EnAccess/Cicada-GSM-HW/design/source/ltspice/Power.asc

C1: cap; 680µ
C2: cap; 680µ
C3: cap; 680µ
C4: cap; 680µ
C5: cap; 10µF
C6: cap; 10µF
C7: cap; 470p
C8: cap; 220µ
C9: cap; 220µ
C10: cap; 220µ
C11: cap; 10µF
D2: schottky; SS24
I1: load; PULSE(0.01A 2A 20ms 0 0 577us 5.192ms 1000)
L1: ind; 220µ; Rser=.1
R1: res; .08
R2: res; 0.08
R3: res; 0.08
R4: res; 0.08
R5: res; 0.02
R6: res; 0.02
R7: res; 1000
R8: res; 500
R9: res; .5
R10: res; 3600
R11: res; 1200
R12: res; .2
R13: res; .2
R14: res; .2
R15: res; .1
R16: res; 0.01
U1: LT1086H
U2: mc34063
V1: voltage; 12; Rser=.5
Named nets: 0
.tran 0 100ms 0 10ns
.inc MC34063.lib
