EnAccess/Cicada-GSM-HW/design/source/ltspice/MC34063_buck.asc

C1: polcap; 220µ; Rser=0.1
C2: cap; 470p
C3: polcap; 220µ; Rser=0.1
D1: schottky; 1N5819
I1: load2; 0.5m
L1: ind2; 220µ; Rser=0.5
R1: res; 0.33
R2: res; 3.6k
R3: res; 1.2k
R4: res; 10
U1: mc34063
V1: voltage; 25; Rser=0.3
Named nets: 0, Vo, ct, swe, vdd, cinv, swc
.tran 0 2m 1u 100n uic
.inc MC34063.lib
.options Gmin=1e-9  method=Gear
A DC/DC BUCK CONVERTER WITH A MOTOROLA MC34063
Test circuit and models from Helmut Sennewald    03/14/2004
The symbol is from Drew.
 
Don't remove this copyright notice.
The used models are property of ONSEMI and/or  Intusoft(www.intusoft.com).
They are from ONsemi's webpage and also from the Intusoft's SPICE (ICAP/4 demo 8.3.10).
The links are www.onsemi.com and www.intusoft.com .
 
 
Three of the models have been modified to LTSPICE syntax.
The PSPICE model runs without** any modifiacation in LTSPICE.
So we have now three models available for the 34063 and one model for the MC33063. 
The MC34063 model and the MC34063p model have the closest match, but I don't
know if they best match the real part.
 
    MC34063   (modified* original model included in ICAP/4 demo)
    MC34063p  (original ONsemi PSPICE model) **
    MC34063a  (modified* original ONsemi model for ICAP/4 demo)
    MC33063    (modified* original ONsemi model for ICAP/4 demo) 
 
   *   Means syntax of IF-THEN-ELSE statement adapted to LTSPICE
       All SPICE command lines starting with a comment "*" have been 
       changed to be compatible with LTSPICE. 
      
   ** This has been possible without modification, because no SW(itch) statement 
       has been used.  VT and VH of SW are defined differently in PSPICE.
 
Set the initial conditions of the capacitors C1 and C3 accordingly to your simulation needs.
These are the IC=...  properties of the filter capacitors in the schematic.
